healthinnovation/gorgas_tracker/3D_print_files/Malaria v3.1.jpg

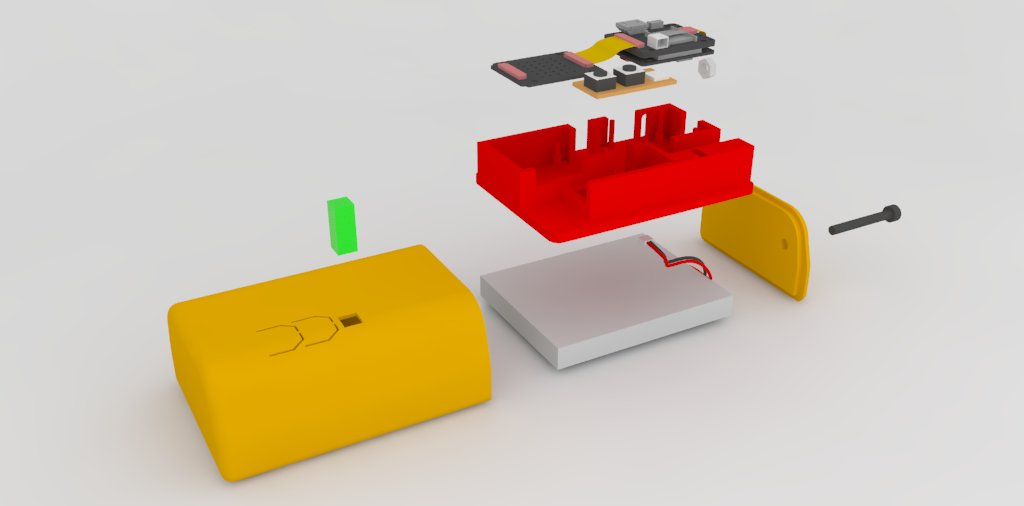
3D_print_files/Malaria v3.1.jpg
