healthinnovation/gorgas_tracker/3D_print_files/Malaria v6.0.jpg

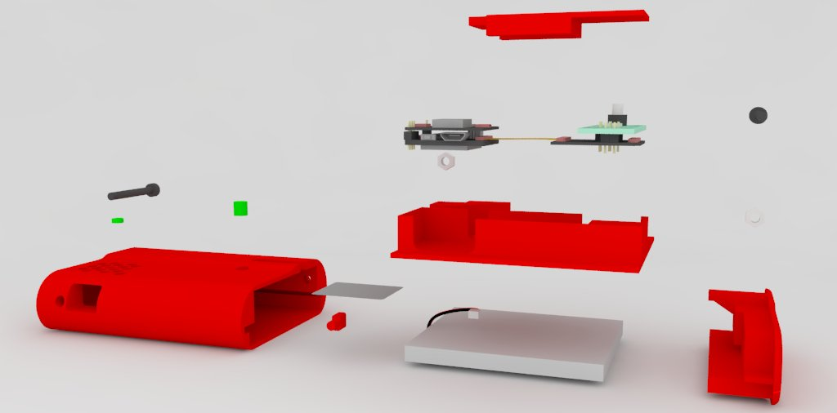
3D_print_files/Malaria v6.0.jpg
